JMBoggess/Split-Flap-Clock/Split Flap/OpenSCAD/jig-flap-hole-v3.scad

translate([25,0])
    cube([15,29,3]);
translate([25,0,3])
    cube([15,3,1.5]);
    
translate([0,14])
    cube([40,15,3]);
translate([0,14,3])
    cube([3,15,1.5]);
