JMBoggess/Split-Flap-Clock/Split Flap/OpenSCAD/jig-flap-split.scad

cube([60, 46, 1.5]);
translate([0,0,1.5])
    cube([60, 3, 1]);
